louisconnell/Quadruped/Solidworks parts/Femur Quadruped.SLDPRT

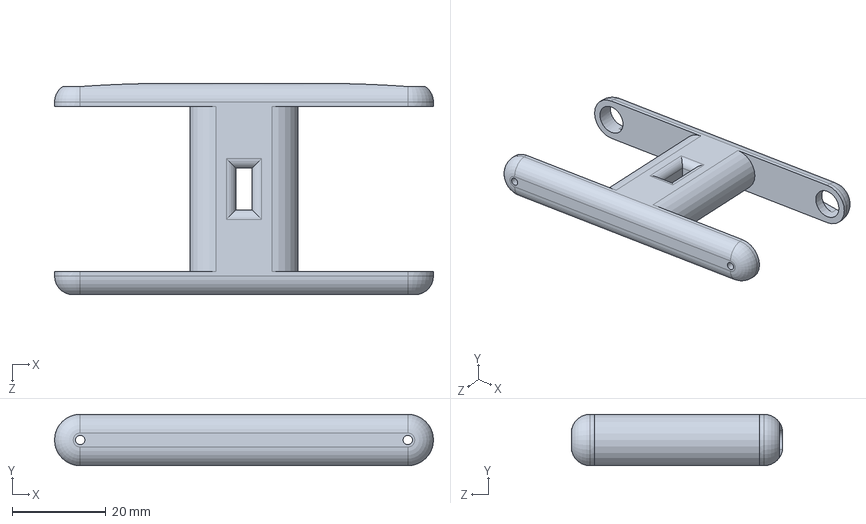
[picture p15: CAD file, 2017-11-06]
Solidworks parts/Femur Quadruped.SLDPRT
81.0 x 11.0 x 45.2 mm
