louisconnell/Quadruped/Solidworks parts/Coxa Quadruped V2.SLDPRT

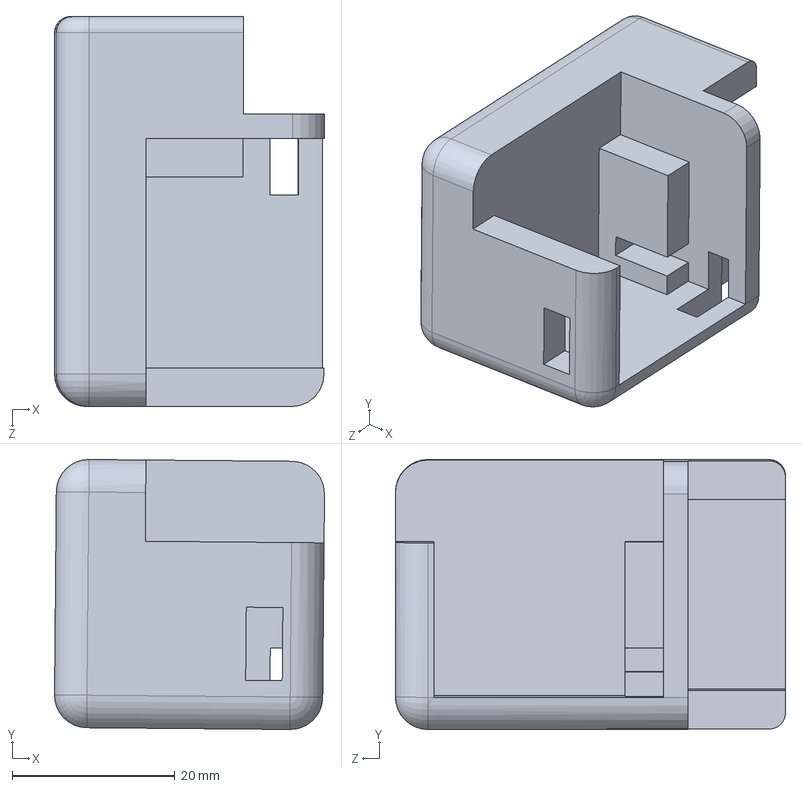
[picture p16: CAD file, 2017-11-06]
Solidworks parts/Coxa Quadruped V2.SLDPRT
33.2 x 33.2 x 48.0 mm
