louisconnell/Quadruped/Solidworks parts/servo motor.SLDPRT

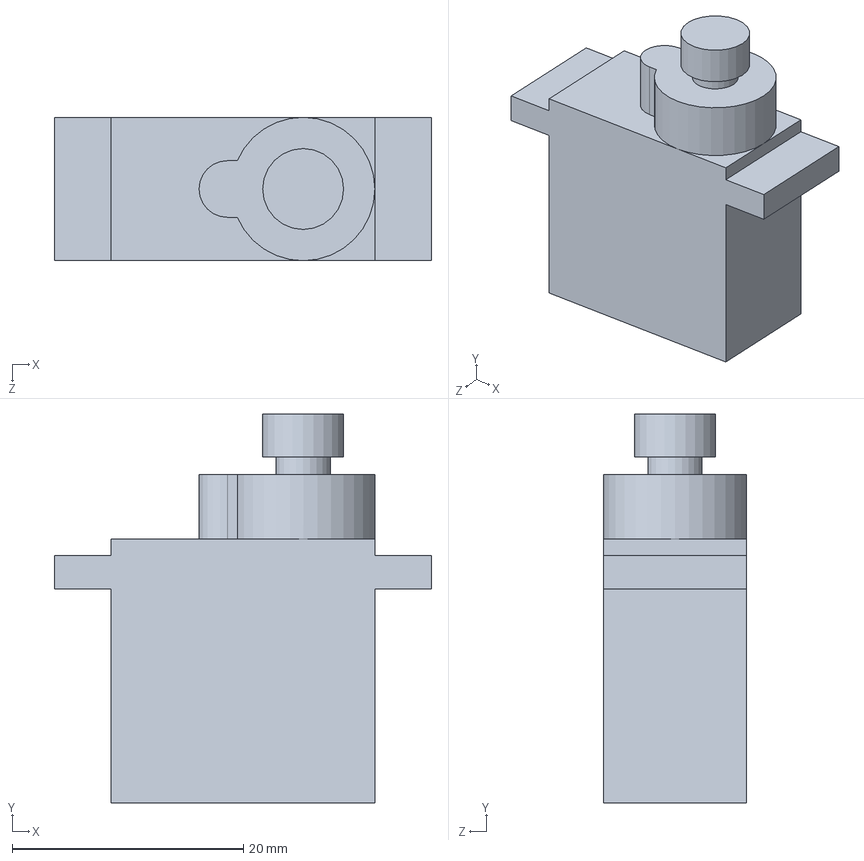
[picture p17: CAD file, 2017-11-06]
Solidworks parts/servo motor.SLDPRT
32.6 x 33.6 x 12.4 mm
