louisconnell/Quadruped/Solidworks parts/Base Quadruped support batterie.SLDPRT

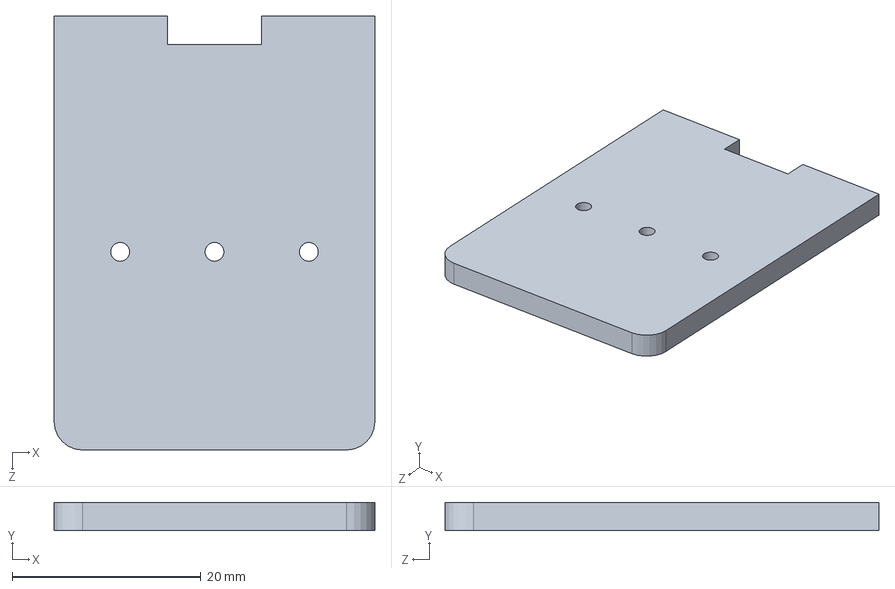
[picture p18: CAD file, 2017-11-06]
Solidworks parts/Base Quadruped support batterie.SLDPRT
34.0 x 3.00 x 46.0 mm
